Pyhesty/ZX-EQ/Board/msxeq_sch.jpg

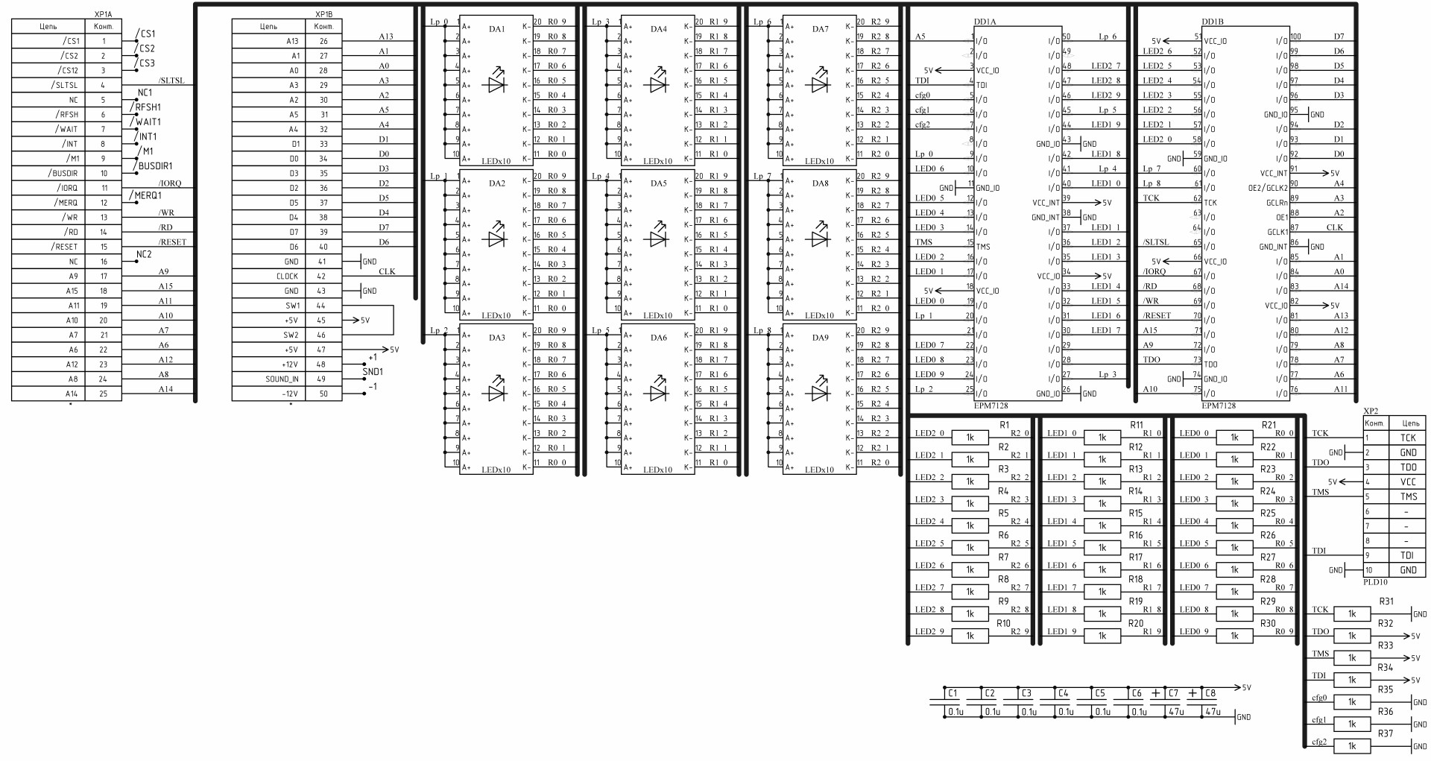
Board/msxeq_sch.jpg
