Pyhesty/ZX-EQ/Img4Posts/PCBinPlate.jpg

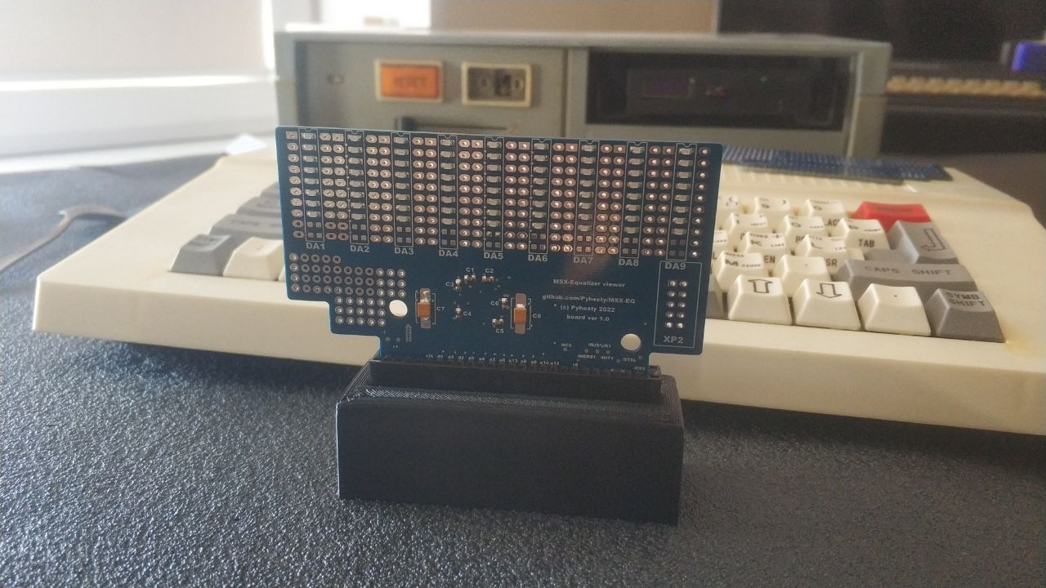
Img4Posts/PCBinPlate.jpg
