Pyhesty/ZX-EQ/Img4Posts/ZXEQ_Case.jpg

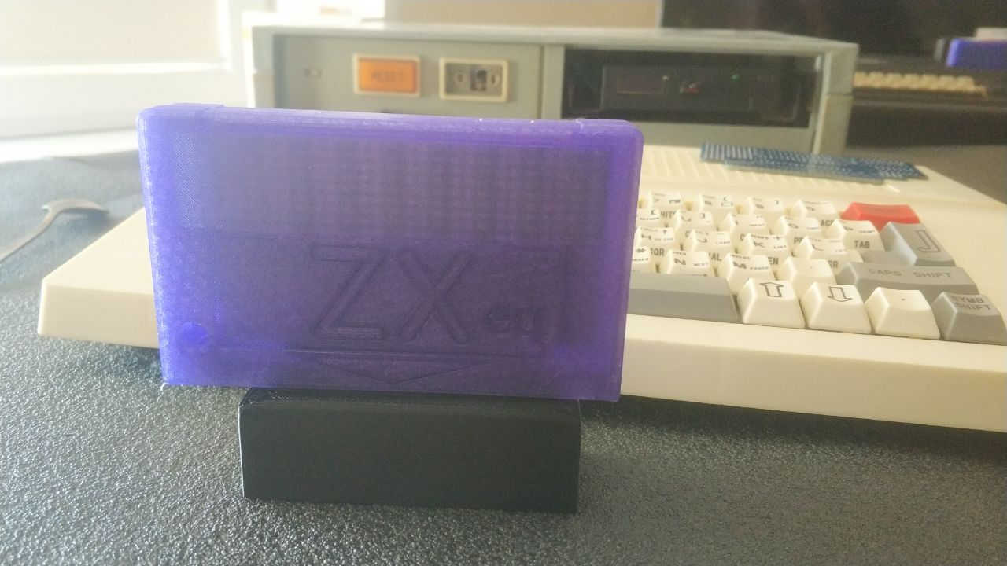
Img4Posts/ZXEQ_Case.jpg
