Pyhesty/ZX-EQ/Img4Posts/ZXEQ_Plate.jpg

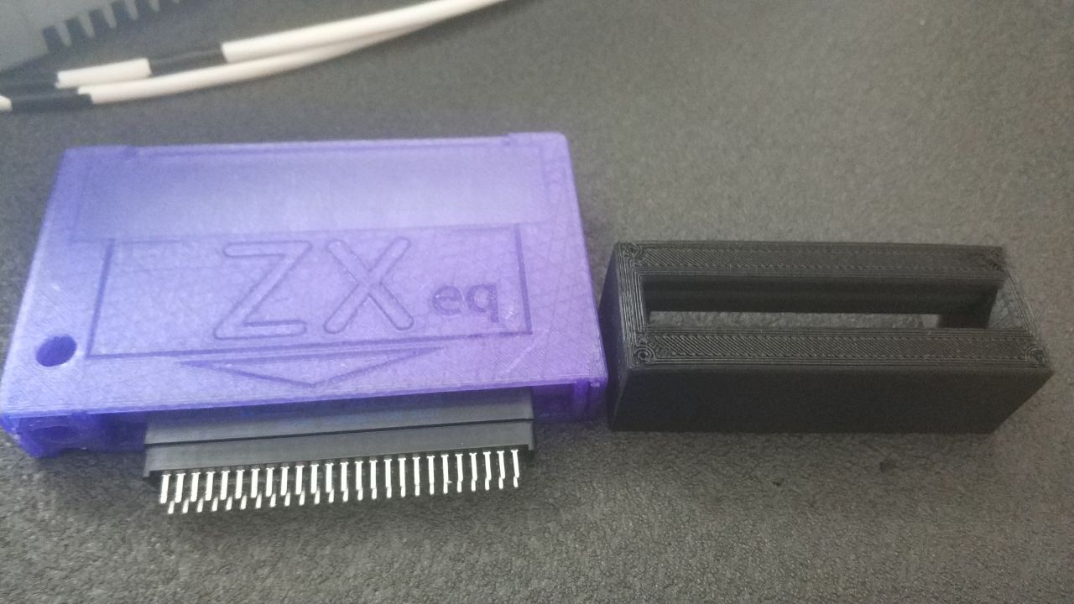
Img4Posts/ZXEQ_Plate.jpg
