Pyhesty/ZX-EQ/Photo/ZXeq_pcb_with_case.jpg

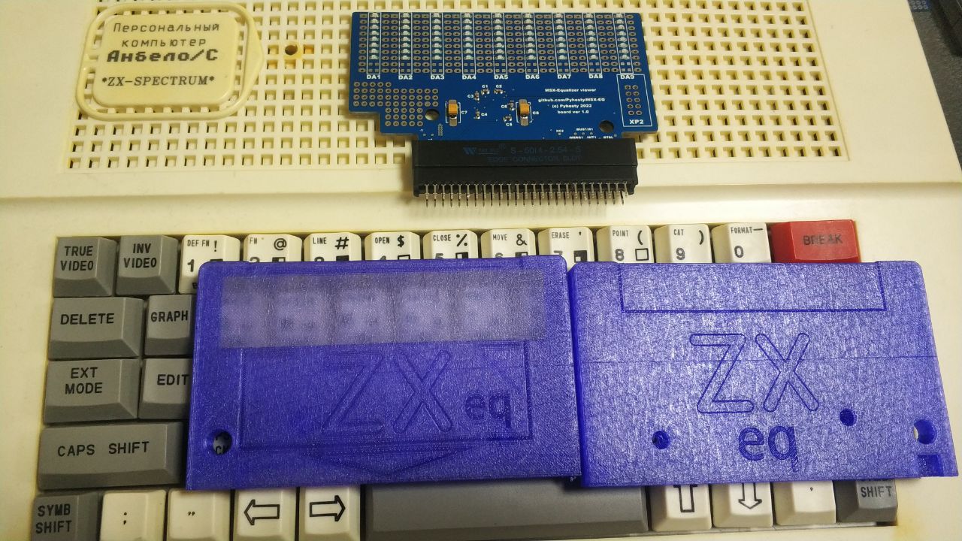
Photo/ZXeq_pcb_with_case.jpg
