Pyhesty/ZX-EQ/Photo/ZXeq_photo2.jpg

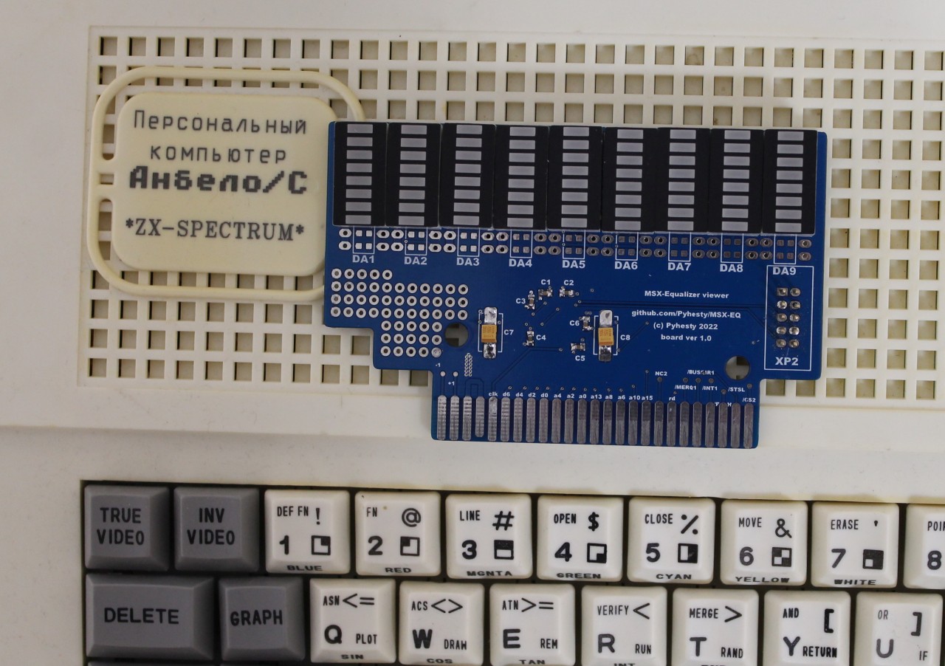
Photo/ZXeq_photo2.jpg
